NamNamIoT/ArduLora/Case box 3D board/Lid_dimentions.png

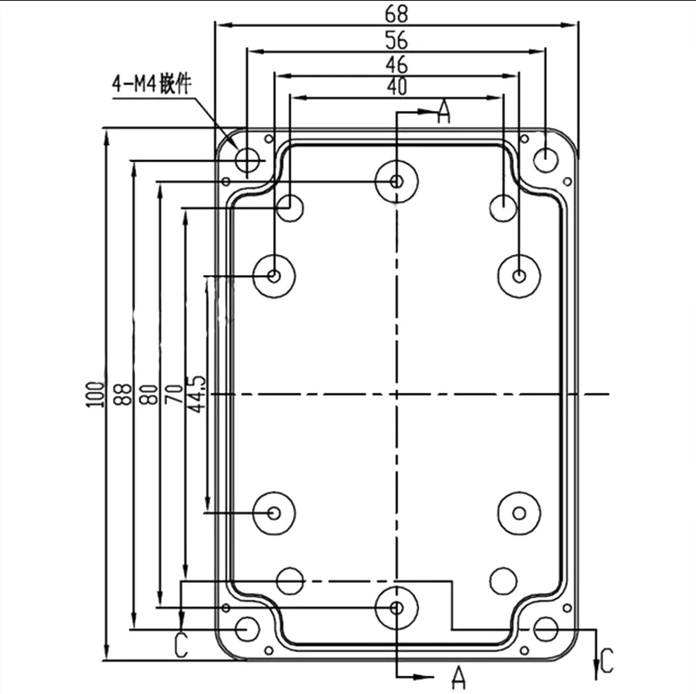
Case box 3D board/Lid_dimentions.png
