NamNamIoT/ArduLora/Case box 3D board/View2.png

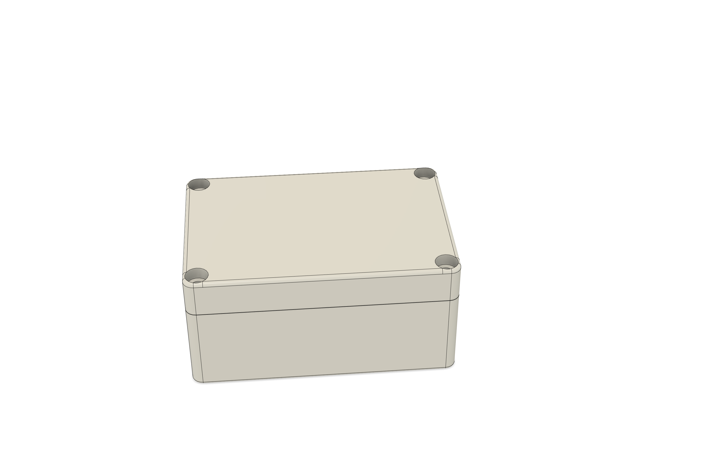
Case box 3D board/View2.png
