NamNamIoT/ArduLora/Case box 3D board/View4.png

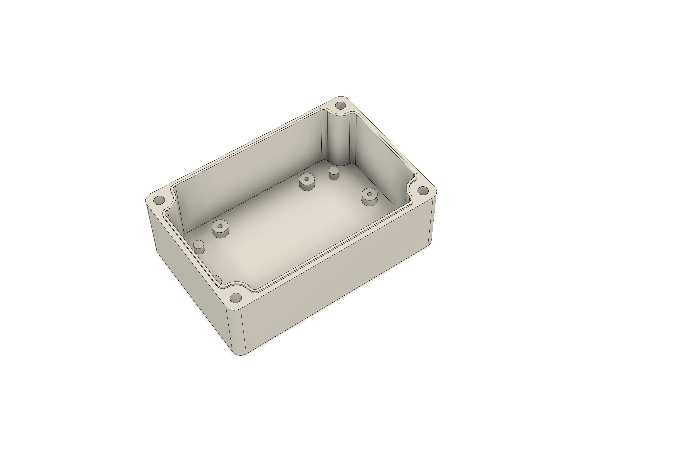
Case box 3D board/View4.png
