NamNamIoT/ArduLora/src/ArduLora_BH1750.h

#ifndef __ARDULORA_BH1750__
#define __ARDULORA_BH1750__

#include <Arduino.h>
#include <Wire.h>

class ArduLora_BH1750 {
    private:
        TwoWire *_wire;
        int _addr;

    public:
        ArduLora_BH1750(int addr = 0x5C, TwoWire *wire = &Wire) ;

        bool begin() ;
        float light() ;

};

#endif
