NamNamIoT/ArduLora/examples/GPS/GPS.ino

#include <ArduLora.h>
#include <TinyGPSPlus.h>

TinyGPSPlus gps; //GPS ATGM336H
void setup() {
  Serial.begin(115200);
  Serial1.begin(9600);
  //Enable power for external sensor
  pinMode(PB5, OUTPUT);
  digitalWrite(PB5, LOW);
  while (Serial1.available()) {
    Serial1.read();
  }
}

void loop() {
  while (Serial1.available() > 0) {
    gps.encode(Serial1.read());
  }
  float gps_lat = gps.location.lat();
  float gps_lng = gps.location.lng();
  float gps_speed = gps.speed.mps();
}
